KlausMu/esp32-co2monitor/src/liIonVoltage.cpp

#include "liIonVoltage.h"

#include "config.h"
#include "log.h"

// Prerequisite: calculate factor for your voltage divider
#define VOLTAGEDIV 0.35897436f // 560k/(1M + 560k) voltage divider

// Calibration step 1 (optional):
// Generate lookup table for non-linearity of ESP32 and replace int ADC_LUT[4096] below
// https://github.com/e-tinkers/esp32-adc-calibrate

// Calibration step 2:
// Measure voltage at ESP32 pin with external instrument. See in log file which analog value was read (uncomment logging in void liIonVoltage_update() below)
#define VOLTAGEREF 1.28f       // this voltage was set at pin, measured with external instrument ...
#define ANALOGVALUEREF 2867    // when this value was read at input PIN

// Calibration step 3:
// Measure voltage at battery and compare with the result shown in device. Calculate correction factor if needed.
#define correction 0.9778f     // factor that has to be applied to the final voltage value to get most precise values (after applying lookup and divider)

float voltage=0.0;
byte batterystate=0;

uint16_t analogValue;
float analogValueLookup;
float analogValueSumLookup;

int ADC_LUT[4096] = { 0,
33,36,38,41,43,46,48,49,51,52,53,54,56,57,58,59,
61,62,63,64,65,66,67,68,68,69,70,71,72,73,73,74,
75,76,77,78,78,79,80,82,83,84,86,87,89,90,91,93,
94,96,97,98,99,100,101,102,103,104,105,106,107,108,109,110,
111,112,113,114,115,117,118,119,121,122,123,125,126,127,128,129,
130,131,132,133,134,135,136,137,138,139,140,141,142,143,144,145,
146,147,148,149,151,152,153,154,155,156,157,158,159,160,161,162,
164,165,166,167,168,169,170,171,173,174,175,176,177,178,179,181,
182,183,184,185,186,187,189,190,191,192,193,194,195,196,197,198,
199,200,201,202,203,204,205,206,207,208,209,210,211,212,213,213,
214,215,216,217,218,219,220,4095,221,222,223,224,225,227,228,230,
231,232,234,4095,237,238,240,241,242,244,245,246,248,249,250,252,
4095,254,255,257,257,258,259,260,261,262,263,264,4095,266,267,268,
269,269,270,271,272,274,275,276,277,278,279,280,281,282,284,285,
286,287,288,289,290,291,292,293,294,295,296,296,297,298,299,300,
301,302,303,304,305,306,307,308,309,310,311,312,313,314,315,316,
4095,318,319,321,322,323,324,325,327,328,329,330,332,333,334,335,
336,337,338,339,340,341,342,343,344,345,346,347,348,349,350,351,
352,353,354,356,357,358,359,360,361,362,363,364,365,366,367,368,
370,371,372,373,375,376,377,379,380,381,383,384,385,386,387,388,
389,390,391,392,393,394,395,396,397,398,399,400,401,403,404,405,
406,408,409,410,412,413,414,415,416,417,418,419,420,420,421,422,
423,424,425,425,426,427,428,429,429,430,431,432,433,434,435,436,
437,438,439,440,442,443,444,445,446,447,448,449,451,452,454,455,
457,458,460,461,462,464,465,467,468,469,471,472,473,475,476,478,
479,480,481,482,482,483,484,485,485,486,487,488,488,489,490,491,
491,492,493,494,494,495,496,498,500,502,503,505,507,509,510,512,
513,514,515,516,516,517,518,519,520,521,522,523,524,525,526,526,
527,528,530,531,533,534,535,537,538,539,541,542,543,4094,546,547,
548,549,550,551,552,553,554,555,556,558,559,560,561,562,563,563,
564,565,566,567,568,569,570,571,572,573,574,575,576,577,578,579,
581,582,583,584,585,587,588,589,590,592,592,593,594,595,595,596,
4094,597,598,599,600,600,601,602,602,603,604,604,605,606,607,607,
608,609,610,611,612,613,614,615,616,617,618,619,620,621,622,623,
624,626,627,628,629,631,632,633,635,636,637,638,640,641,642,644,
645,646,648,649,650,652,653,654,656,657,658,659,660,661,662,663,
664,665,666,667,668,669,670,671,672,673,674,675,677,678,679,680,
682,683,684,685,687,688,689,690,691,692,693,693,694,695,696,697,
698,699,700,701,702,703,704,705,706,707,708,710,711,712,713,714,
715,717,718,719,720,721,722,724,725,726,727,728,729,730,731,733,
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
} ;

void calculateBatterystate() {
  // This mapping from voltage to batterystate is always somehow inaccurate. These are the values I measured at my 18650.
  // It is only valid while discharging, not while charging.
  if (voltage >= 4.100) {
    batterystate = 100;
  } else if (voltage >= 3.982) {
    batterystate = 90;
  } else if (voltage >= 3.888) {
    batterystate = 80;
  } else if (voltage >= 3.802) {
    batterystate = 70;
  } else if (voltage >= 3.706) {
    batterystate = 60;
  } else if (voltage >= 3.610) {
    batterystate = 50;
  } else if (voltage >= 3.557) {
    batterystate = 40;
  } else if (voltage >= 3.508) {
    batterystate = 30;
  } else if (voltage >= 3.440) {
    batterystate = 20;
  } else if (voltage >= 3.339) {
    batterystate = 10;
  } else {
    batterystate = 2;
  };
}

void liIonVoltage_setup() {
  pinMode(VOLTAGE_PIN, INPUT);
  // ADC_6db is best for values between 150..1750 mV at input PIN
  // https://docs.espressif.com/projects/esp-idf/en/latest/esp32/api-reference/peripherals/adc.html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 
  // With the voltage divider from above, we expect 4.2V * VOLTAGEDIV = 1.5 V maximum voltage at input PIN
  analogSetAttenuation(ADC_6db);
  Log.printf("  Voltage measurement sucessfully initialized.\r\n");
}

void liIonVoltage_update() {

  float voltageOld = voltage;
  byte batterystateOld = batterystate;

  int i=0;
  voltage=0;
  analogValueSumLookup=0.0;
  for(i=0;i<10;i++) {
      analogValue = analogRead(VOLTAGE_PIN);
      // Log.printf("analogValue read for voltage: %d\r\n", analogValue);
      
      analogValueLookup = ADC_LUT[analogValue];
      analogValueSumLookup += analogValueLookup;
      voltage += (float(analogValueLookup) / ANALOGVALUEREF )*VOLTAGEREF / VOLTAGEDIV * correction;
  }
  voltage /= 10;
  voltage = floor(voltage*100 + 0.5) / 100;

  calculateBatterystate();
  
  if ((voltageOld != voltage) || (batterystateOld != batterystate)) {
    Log.printf("Voltage: %.2fV, Battery state: %d%%\r\n", voltage, batterystate);
  }
}
